smdjeff/DE10Jamma/PXL_20250718_165605434.jpg

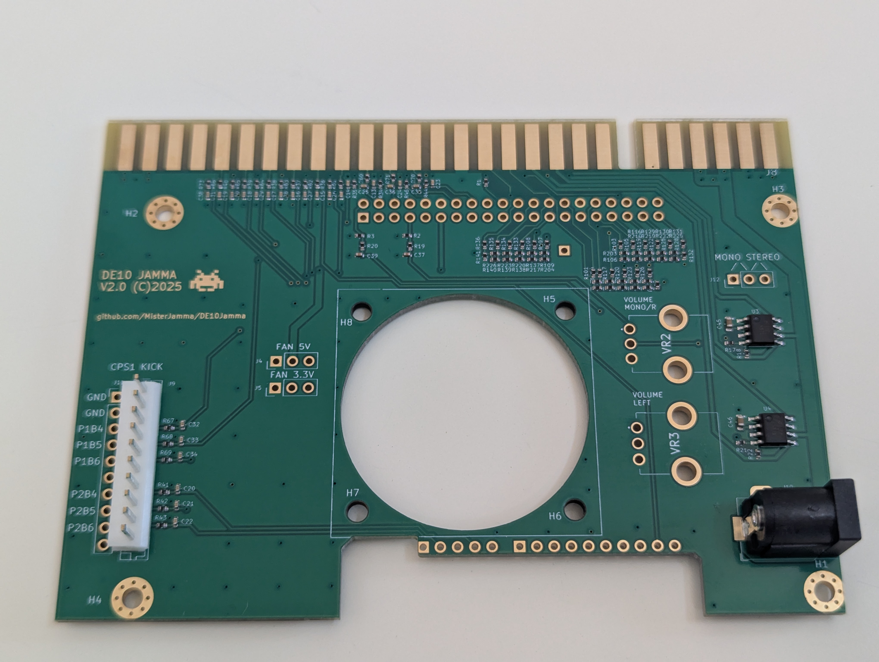
PXL_20250718_165605434.jpg
